tonykoop/flutes/CAD/Native American Flutes/FLUTES 10.jpg

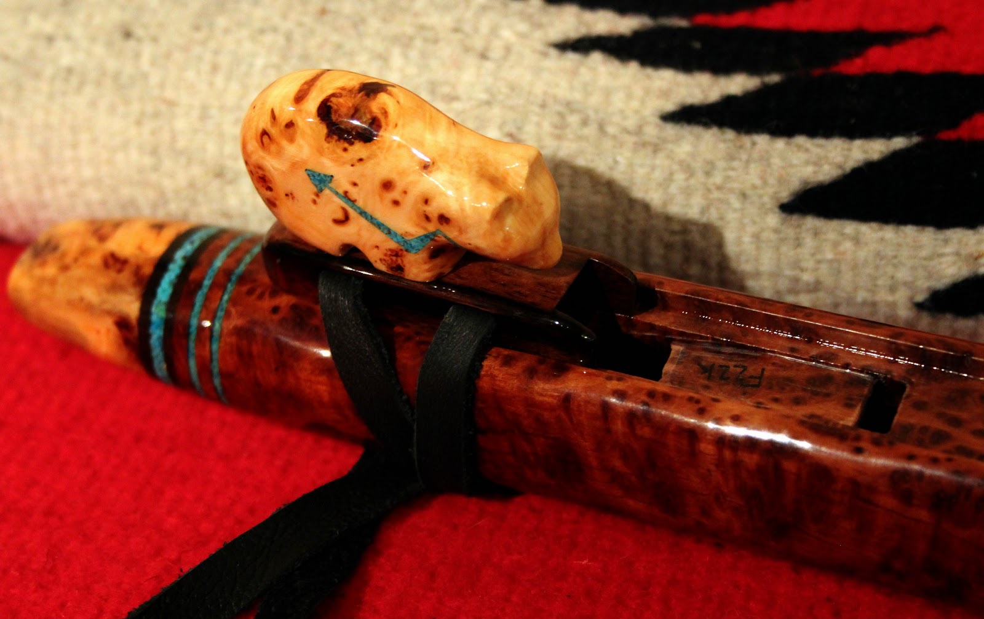
CAD/Native American Flutes/FLUTES 10.jpg
