tonykoop/flutes/images/2021-09-22 11.50.19.jpg

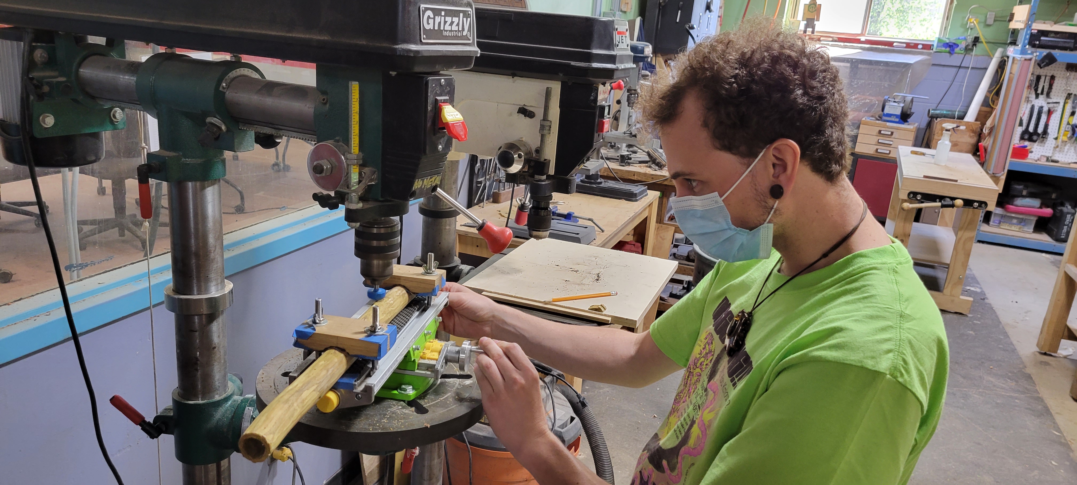
images/2021-09-22 11.50.19.jpg
