tonykoop/flutes/images/2021-09-22 13.02.19.jpg

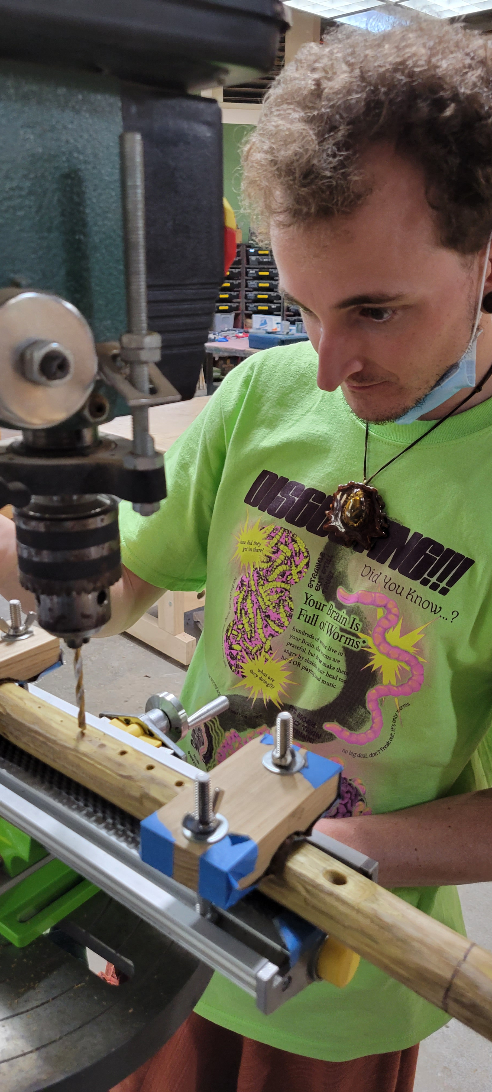
images/2021-09-22 13.02.19.jpg
