tonykoop/flutes/images/20200102_101700.jpg

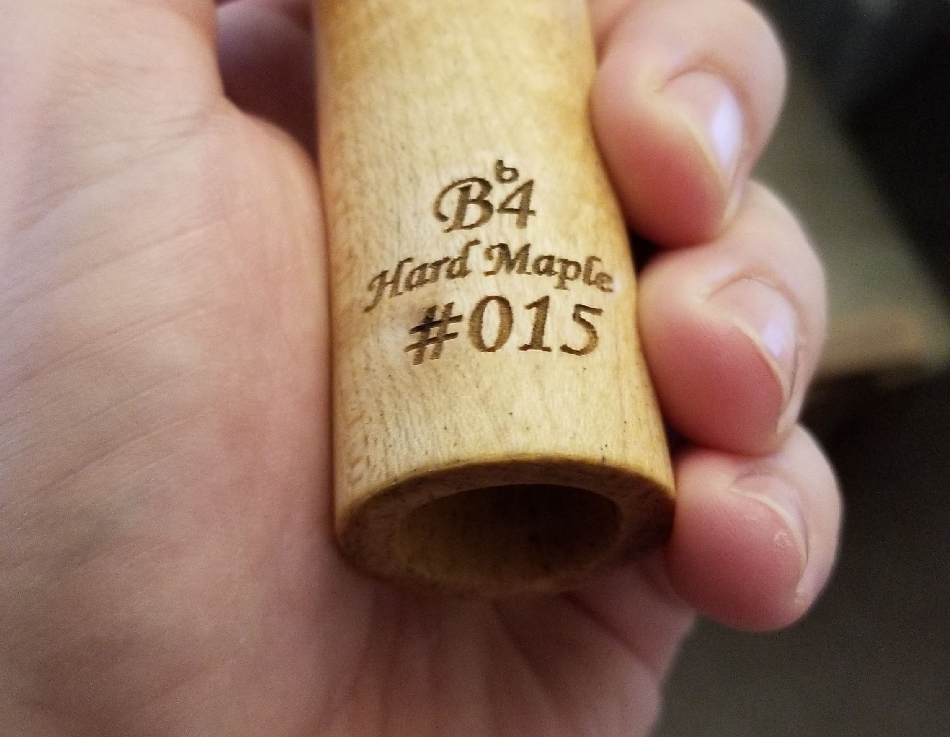
images/20200102_101700.jpg
