tonykoop/flutes/images/20200103_151445.jpg

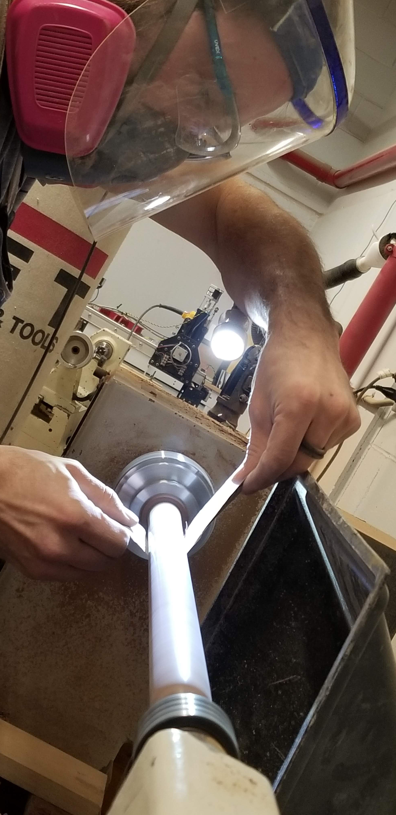
images/20200103_151445.jpg
