tonykoop/flutes/images/20200106_140247.jpg

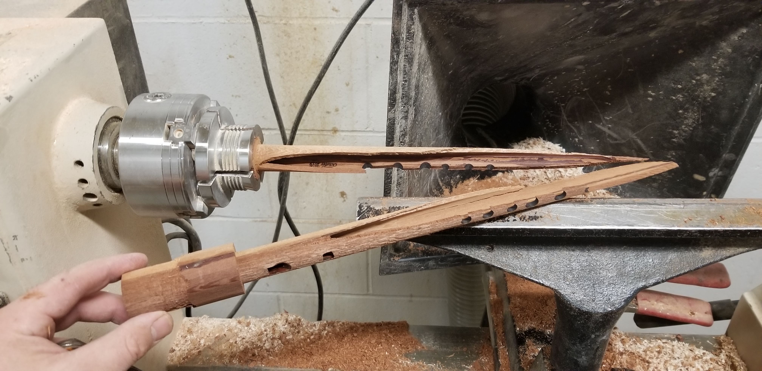
images/20200106_140247.jpg
