tonykoop/flutes/images/20200119_165358.jpg

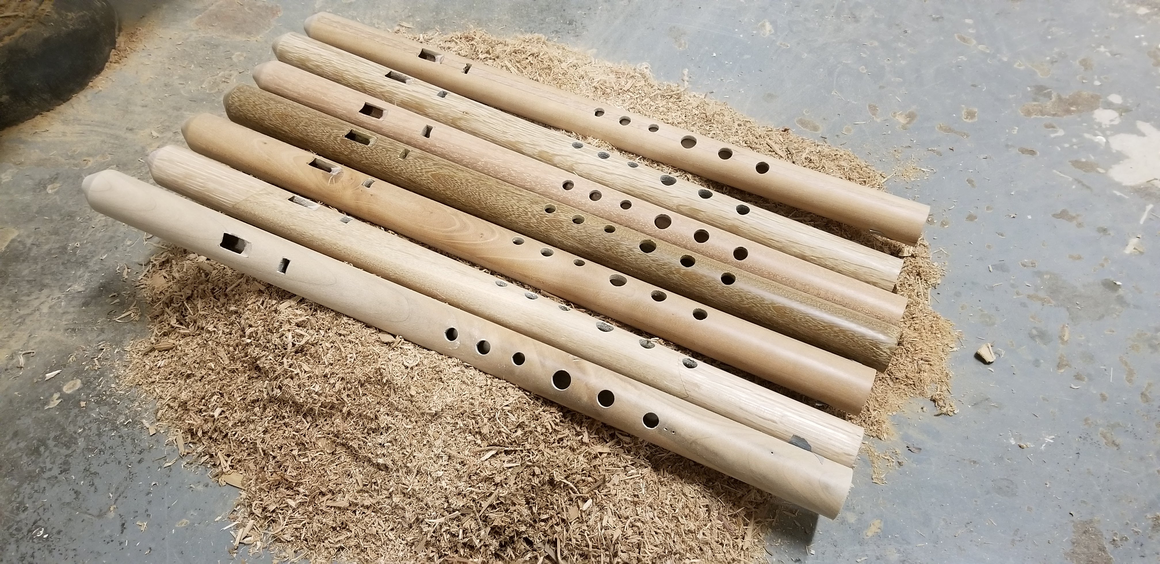
images/20200119_165358.jpg
