tonykoop/flutes/images/20200119_203253.jpg

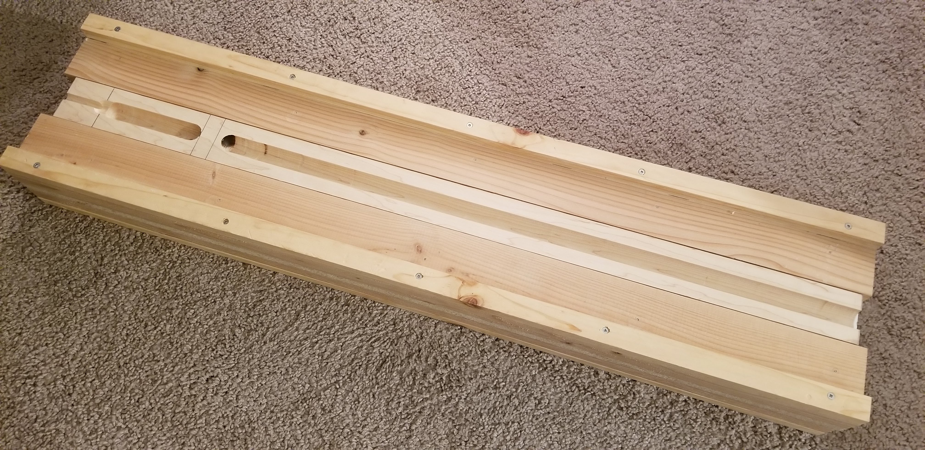
images/20200119_203253.jpg
