tonykoop/flutes/images/20200121_170148.jpg

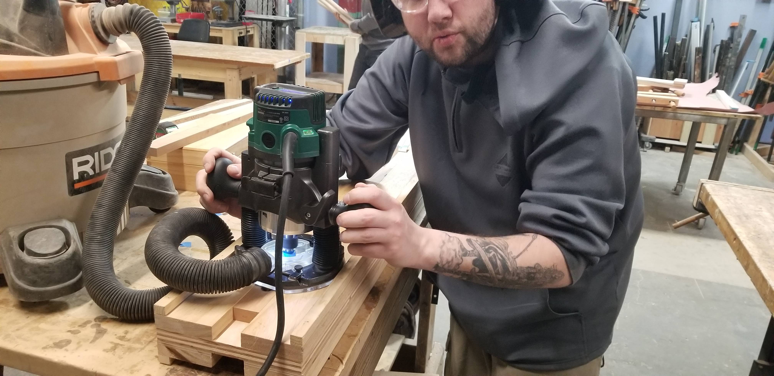
images/20200121_170148.jpg
