tonykoop/flutes/images/20200315_233502.jpg

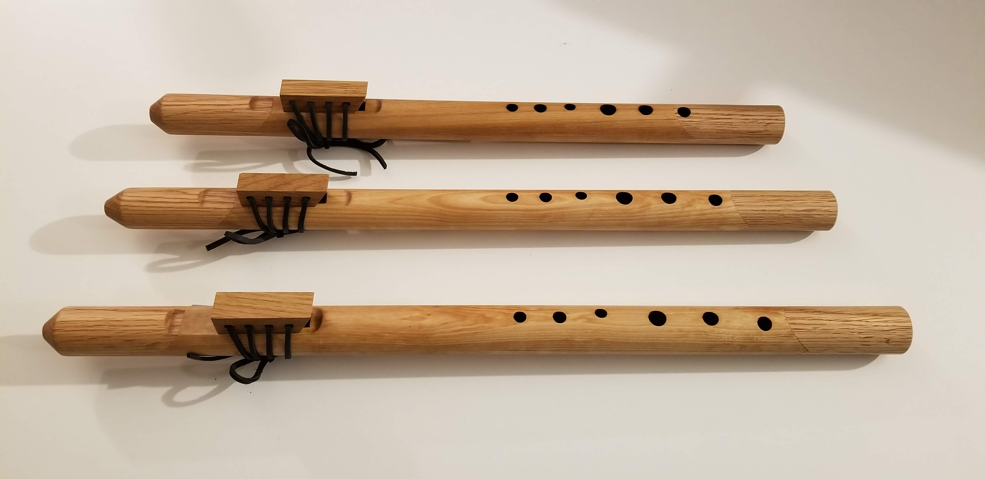
images/20200315_233502.jpg
