tonykoop/flutes/images/family-group.png

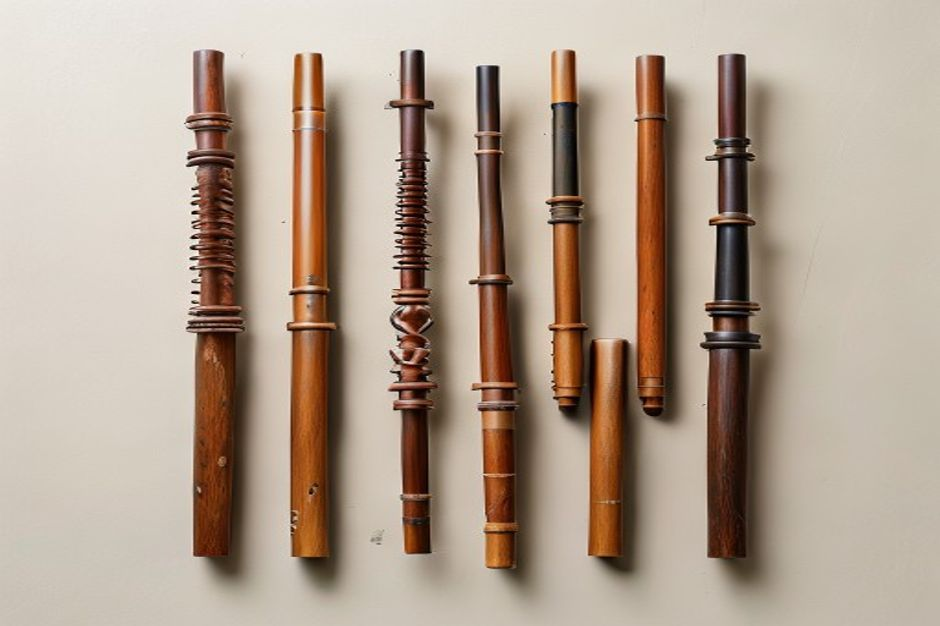
images/family-group.png
