tonykoop/flutes/images/IMG_20190920_092615_140.jpg

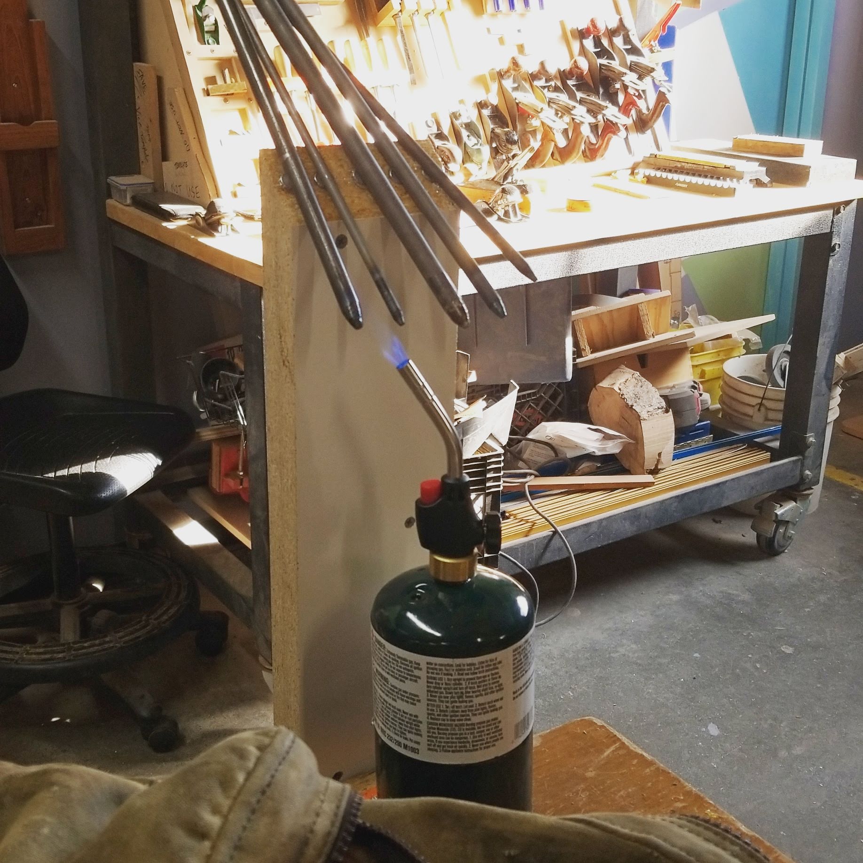
images/IMG_20190920_092615_140.jpg
