tonykoop/flutes/images/IMG_20200206_195046.jpg

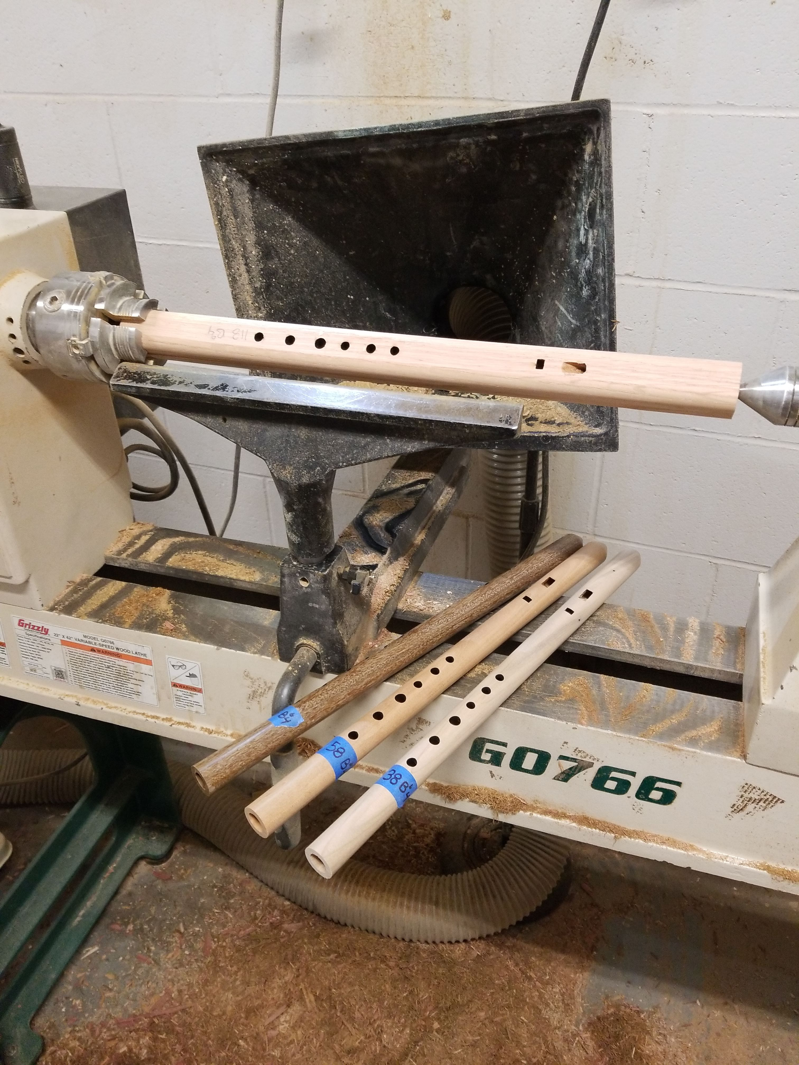
images/IMG_20200206_195046.jpg
