tonykoop/flutes/images/IMG_20200323_135345_026.jpg

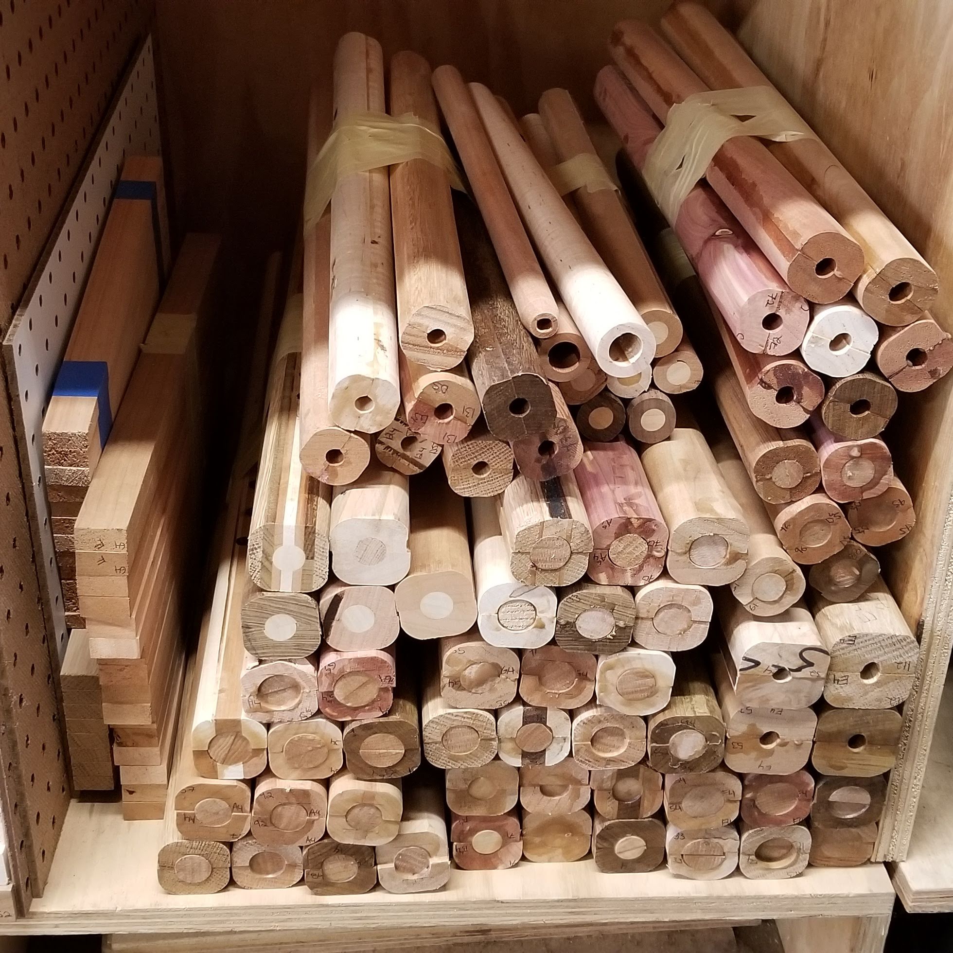
images/IMG_20200323_135345_026.jpg
