tonykoop/flutes/Screenshot 2026-05-02 150708.png

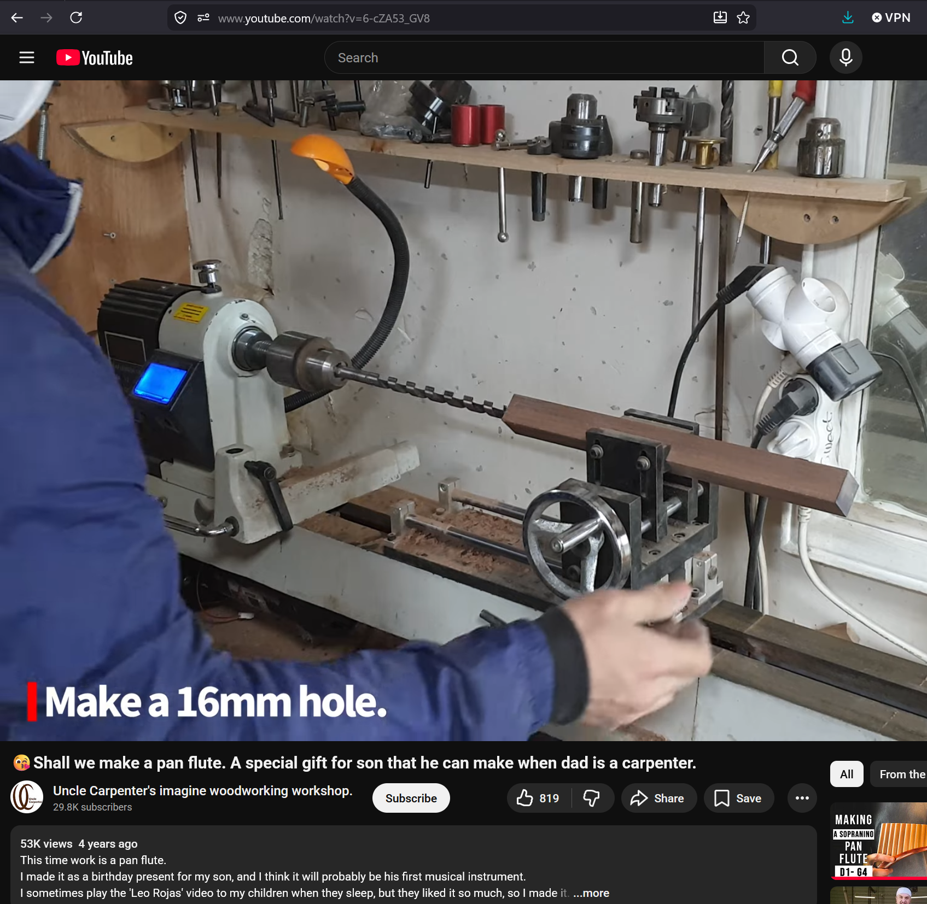
Screenshot 2026-05-02 150708.png
